redstoner-35/Xtern-Ripper/img/2.jpg

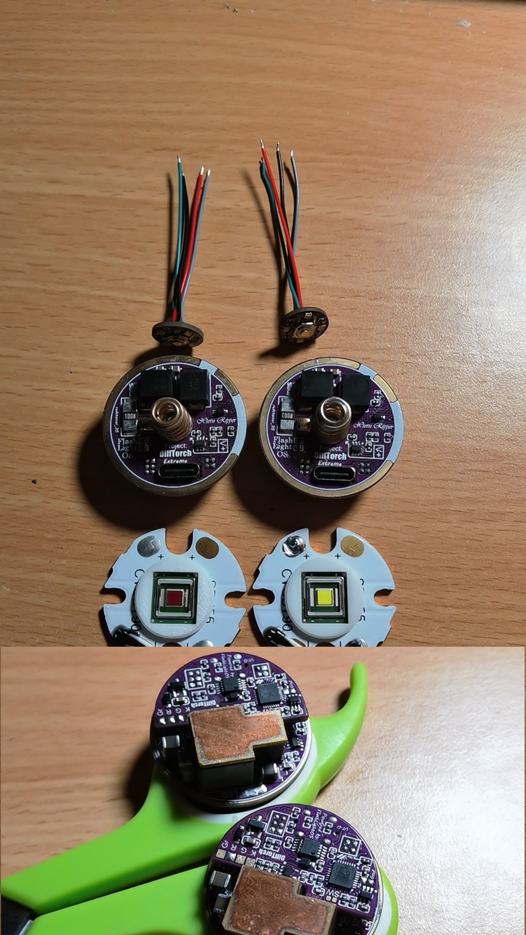
img/2.jpg
