redstoner-35/Xtern-Ripper/img/3.jpg

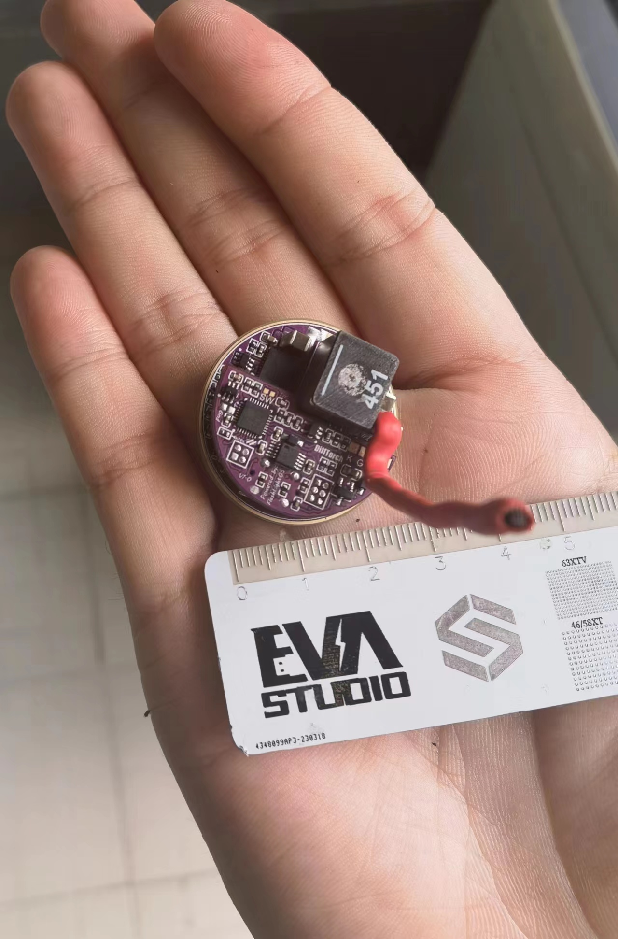
img/3.jpg
