redstoner-35/Xtern-Ripper/img/wx_camera_1691152957961.jpg

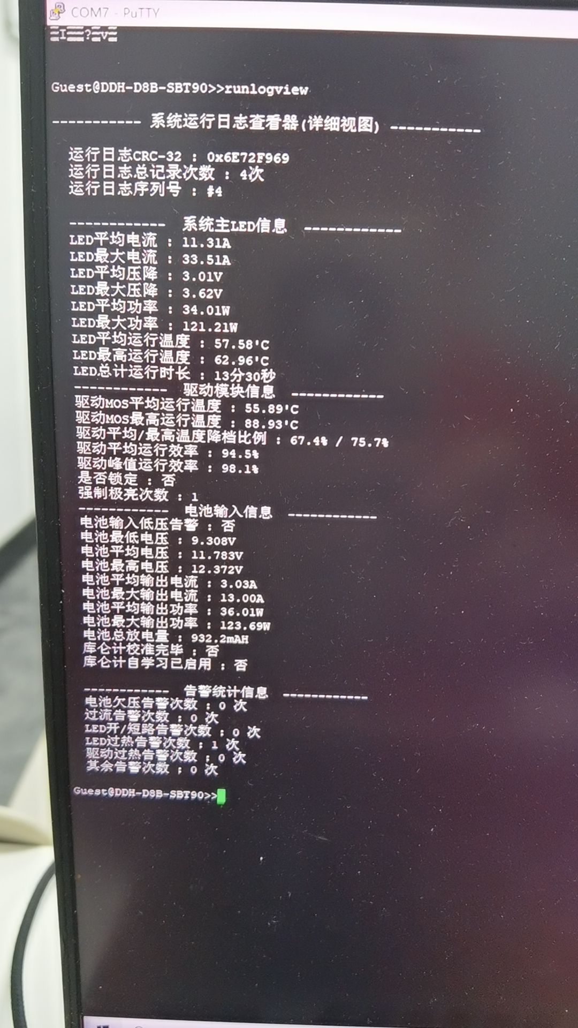
img/wx_camera_1691152957961.jpg
