redstoner-35/Xtern-Ripper/img/wx_camera_1691343480557.jpg

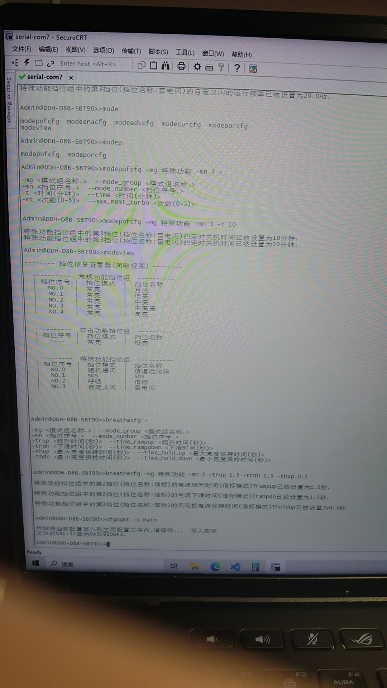
img/wx_camera_1691343480557.jpg
